PiKeeb/fu-keyboard/pcb_files/kicad_project/fu_keyboard.kicad_sch

## KiCad design pcb_files/kicad_project/fu_keyboard.kicad_sch (2021-12-26)

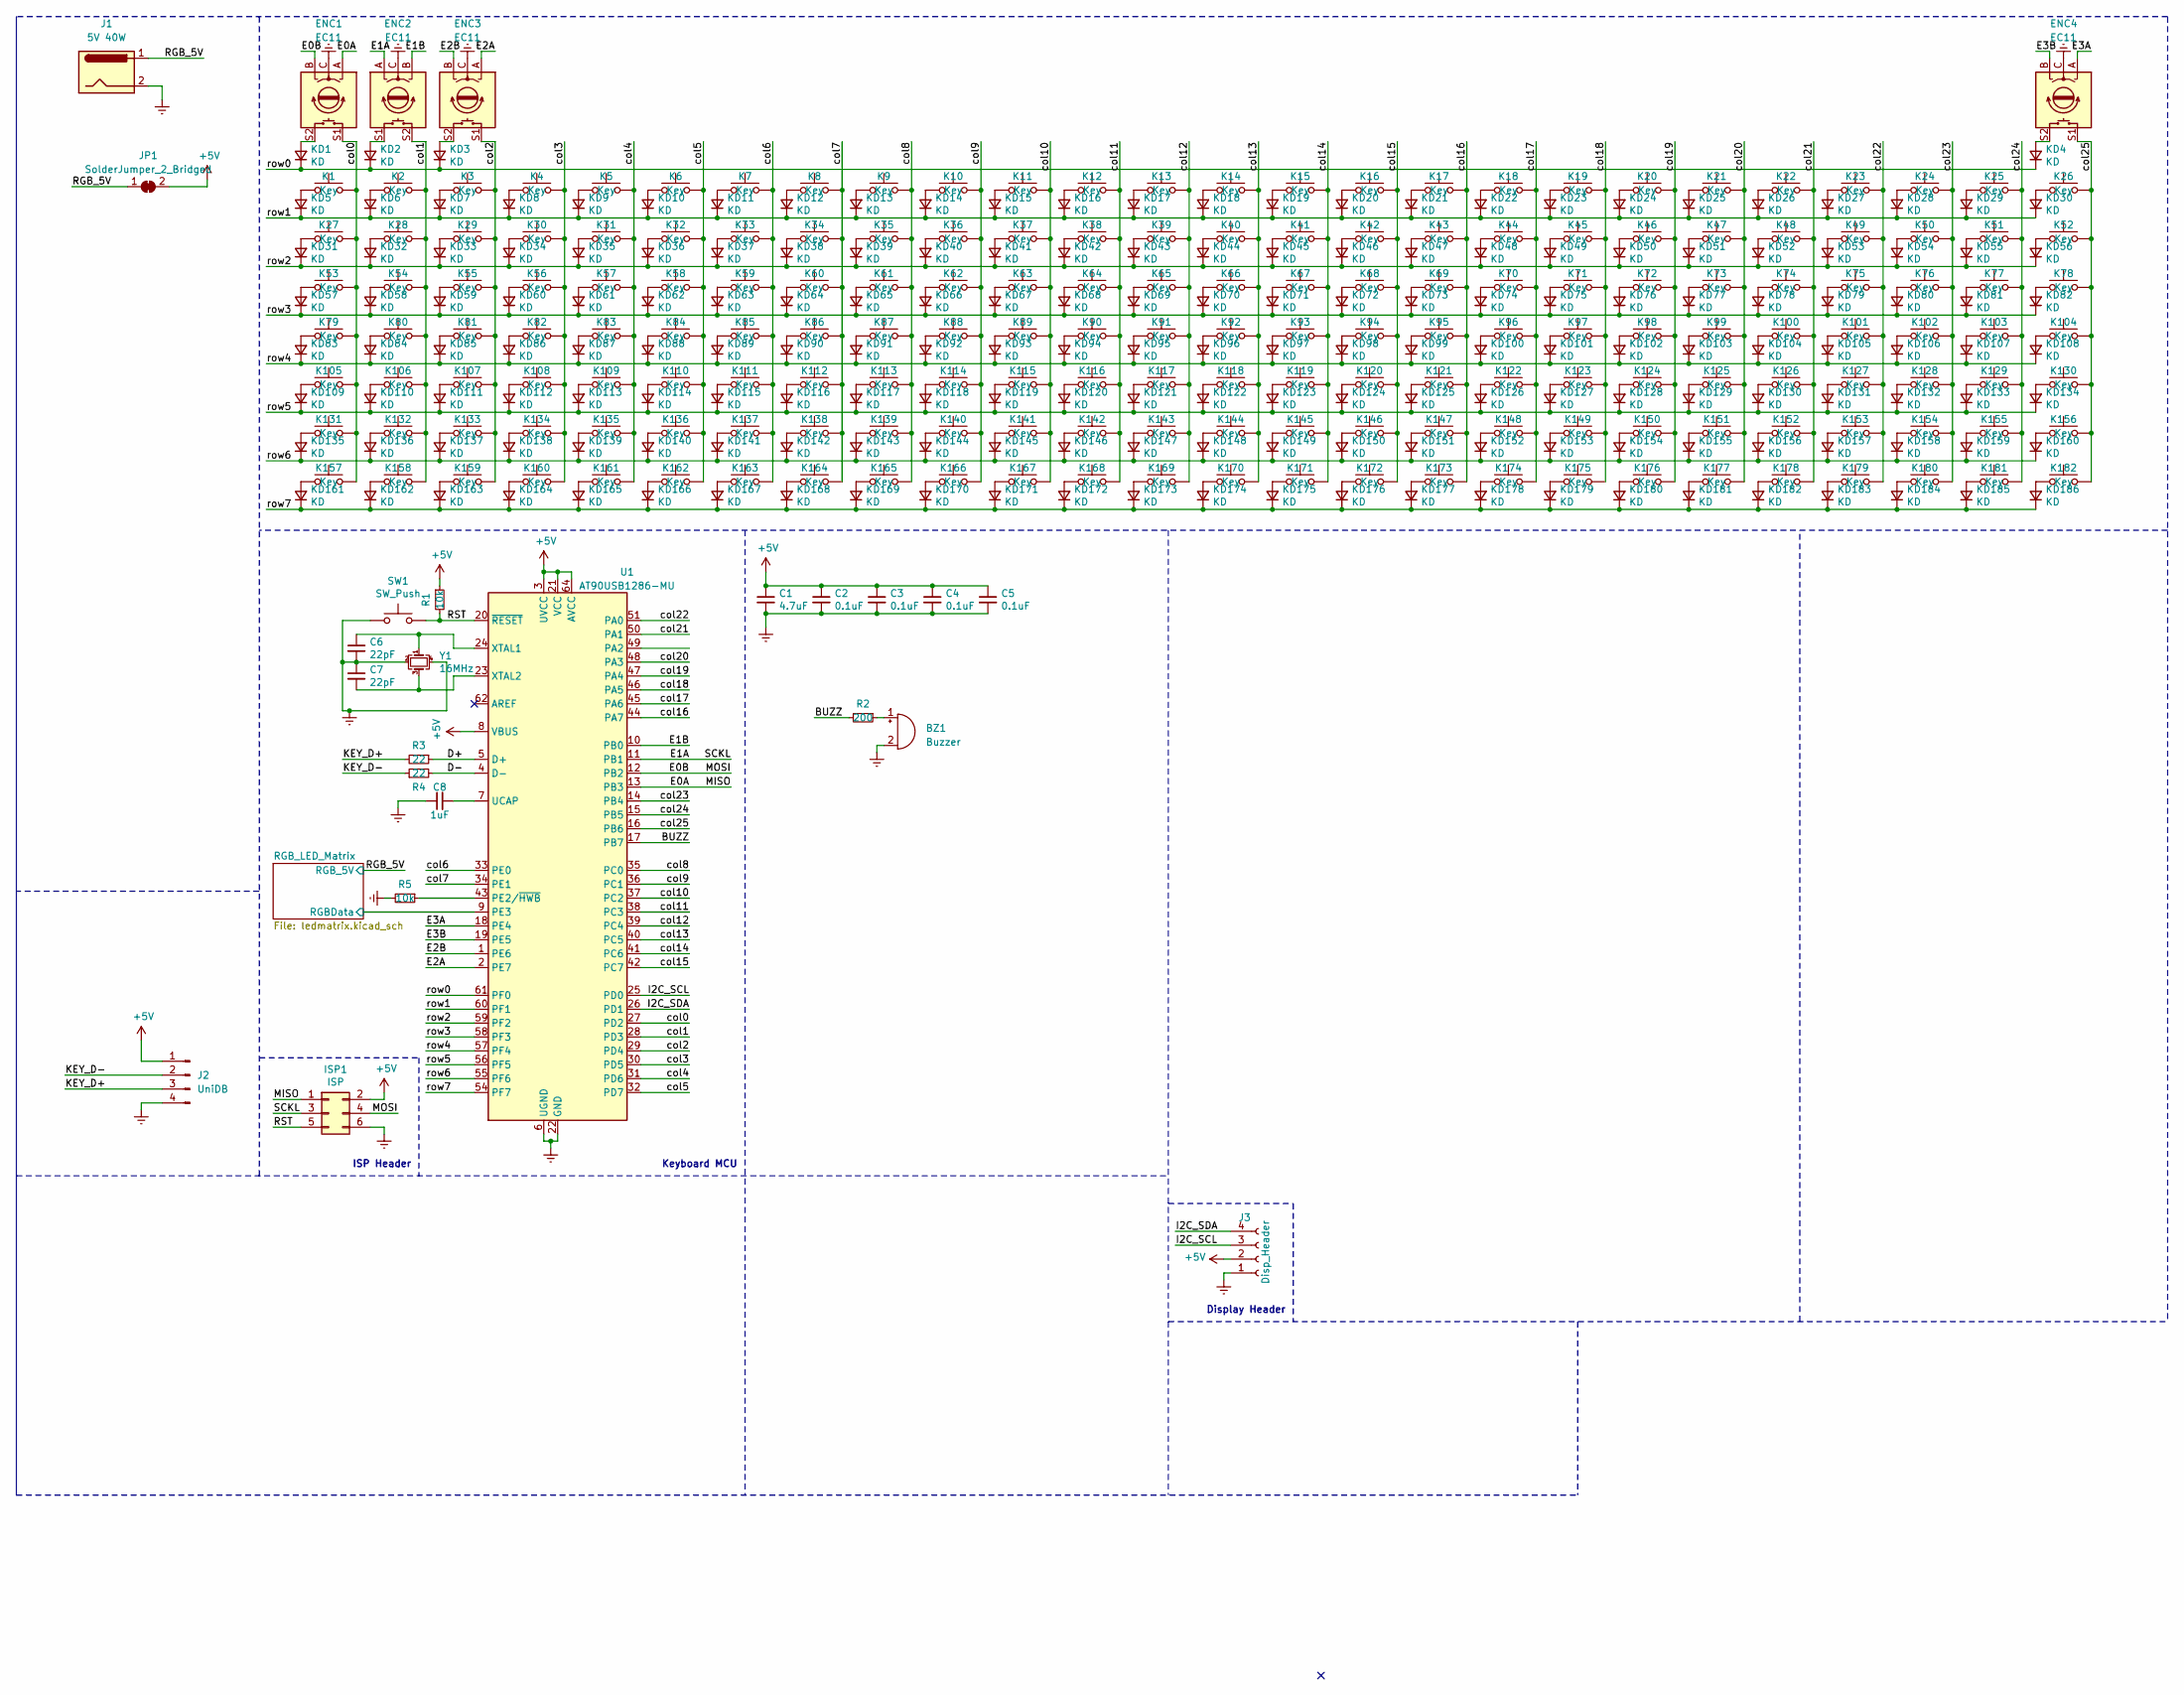
[picture p6: schematic fu_keyboard.kicad_sch]

Parts:
BZ1: Buzzer; Buzzer_CUI_CPT-9019S-SMT
C1: 4.7uF; C_0603_1608Metric
C2, C3, C4, C5: 0.1uF; C_0603_1608Metric
C6, C7: 22pF; C_0603_1608Metric
C8: 1uF; C_0603_1608Metric
ENC1, ENC2, ENC3, ENC4: EC11; RotaryEncoder_Alps_EC11E-Switch_Vertical_H20mm_CircularMoun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
ISP1: ISP; PinHeader_2x03_P2.54mm_Vertical
J1: 5V 40W; DC-058A-D010
J2: UniDB; JST_SH_SM04B-SRSS-TB_1x04-1MP_P1.00mm_Horizontal
J3: Disp_Header; Generic_SSD1306_0.91inch
JP1: SolderJumper_2_Bridged; SolderJumper-2_P1.3mm_Bridged2Bar_RoundedPad1.0x1.5mm
K1, K2, K3, K4, K5, K6, K7, K8, K9, K10, K11, K12, K13, K14, K15, K16, K17, K18, K19, K20, K21, K22, K23, K24, K25, K26, K27, K28, K29, K30, K31, K32, K33, K34, K35, K36, K37, K38, K39, K40, K41, K42, K43, K44, K45, K46, K47, K48, K49, K50, K51, K52, K53, K54, K55, K56, K57, K58, K59, K60, K61, K62, K63, K64, K65, K66, K67, K68, K69, K70, K71, K72, K73, K74, K75, K76, K77, K78, K79, K80, K81, K82, K83, K84, K85, K86, K87, K88, K89, K90, K91, K92, K93, K94, K95, K96, K97, K98, K99, K100, K101, K102, K103, K104, K105, K106, K107, K108, K109, K110, K111, K112, K113, K114, K115, K116, K117, K118, K119, K120, K121, K122, K123, K124, K125, K126, K127, K128, K129, K130, K131, K132, K133, K134, K135, K136, K137, K138, K139, K140, K141, K142, K143, K144, K145, K146, K147, K148, K149, K150, K151, K152, K153, K154, K155, K156, K157, K158, K159, K160, K161, K162, K163, K164, K165, K166, K167, K168, K169, K170, K171, K172, K173, K174, K175, K176, K177, K178, K179, K180, K181, K182: Key; Kailh_MX_Socket_1.00u_HoledPads
KD1, KD2, KD3, KD4, KD5, KD6, KD7, KD8, KD9, KD10, KD11, KD12, KD13, KD14, KD15, KD16, KD17, KD18, KD19, KD20, KD21, KD22, KD23, KD24, KD25, KD26, KD27, KD28, KD29, KD30, KD31, KD32, KD33, KD34, KD35, KD36, KD37, KD38, KD39, KD40, KD41, KD42, KD43, KD44, KD45, KD46, KD47, KD48, KD49, KD50, KD51, KD52, KD53, KD54, KD55, KD56, KD57, KD58, KD59, KD60, KD61, KD62, KD63, KD64, KD65, KD66, KD67, KD68, KD69, KD70, KD71, KD72, KD73, KD74, KD75, KD76, KD77, KD78, KD79, KD80, KD81, KD82, KD83, KD84, KD85, KD86, KD87, KD88, KD89, KD90, KD91, KD92, KD93, KD94, KD95, KD96, KD97, KD98, KD99, KD100, KD101, KD102, KD103, KD104, KD105, KD106, KD107, KD108, KD109, KD110, KD111, KD112, KD113, KD114, KD115, KD116, KD117, KD118, KD119, KD120, KD121, KD122, KD123, KD124, KD125, KD126, KD127, KD128, KD129, KD130, KD131, KD132, KD133, KD134, KD135, KD136, KD137, KD138, KD139, KD140, KD141, KD142, KD143, KD144, KD145, KD146, KD147, KD148, KD149, KD150, KD151, KD152, KD153, KD154, KD155, KD156, KD157, KD158, KD159, KD160, KD161, KD162, KD163, KD164, KD165, KD166, KD167, KD168, KD169, KD170, KD171, KD172, KD173, KD174, KD175, KD176, KD177, KD178, KD179, KD180, KD181, KD182, KD183, KD184, KD185, KD186: KD; D_0805_2012Metric
R1, R5: 10k; R_0603_1608Metric
R2: 200; R_0603_1608Metric
R3, R4: 22; R_0603_1608Metric
SW1: SW_Push; SW_SPST_TL3342
U1: AT90USB1286-MU; QFN-64-1EP_9x9mm_P0.5mm_EP7.5x7.5mm
Y1: 16MHz; Crystal_SMD_3225-4Pin_3.2x2.5mm

Connections:
+5V: C1.1, C2.1, C3.1, C4.1, C5.1, ISP1.2, J2.1, J3.2, JP1.2 (B), R1.1, U1.3 (UVCC), U1.8 (VBUS), U1.21 (VCC), U1.52 (VCC), U1.64 (AVCC)
BUZZ: R2.2, U1.17 (PB7)
D+: R3.1, U1.5 (D+)
D-: R4.2, U1.4 (D-)
E0A: ENC1.A, ISP1.1, U1.13 (PB3)
E0B: ENC1.B, ISP1.4, U1.12 (PB2)
E1A: ENC2.A, ISP1.3, U1.11 (PB1)
E1B: ENC2.B, U1.10 (PB0)
E2A: ENC3.A, U1.2 (PE7)
E2B: ENC3.B, U1.1 (PE6)
E3A: ENC4.A, U1.18 (PE4)
E3B: ENC4.B, U1.19 (PE5)
Earth: BZ1.2 (+), C1.2, C2.2, C3.2, C4.2, C5.2, C6.2, C7.1, C8.1, ENC1.C, ENC2.C, ENC3.C, ENC4.C, ISP1.6, J1.2, J2.4, J3.1, R5.2, SW1.1, U1.6 (UGND), U1.22 (GND), U1.53 (GND), U1.63 (GND), U1.65 (GND), Y1.2, Y1.4
I2C_SCL: J3.3, U1.25 (PD0)
I2C_SDA: J3.4, U1.26 (PD1)
KEY_D+: J2.3, R3.2
KEY_D-: J2.2, R4.1
unnamed: BZ1.1 (-), R2.1
unnamed: C6.1, U1.24 (XTAL1), Y1.1
unnamed: C7.2, U1.23 (XTAL2), Y1.3
unnamed: C8.2, U1.7 (UCAP)
unnamed: ENC1.S2, KD1.2 (A)
unnamed: ENC2.S1, KD2.2 (A)
unnamed: ENC3.S2, KD3.2 (A)
unnamed: ENC4.S2, KD4.2 (A)
unnamed: K1.1, KD5.2 (A)
unnamed: K2.1, KD6.2 (A)
unnamed: K3.1, KD7.2 (A)
unnamed: K4.1, KD8.2 (A)
unnamed: K5.1, KD9.2 (A)
unnamed: K6.1, KD10.2 (A)
unnamed: K7.1, KD11.2 (A)
unnamed: K8.1, KD12.2 (A)
unnamed: K9.1, KD13.2 (A)
unnamed: K10.1, KD14.2 (A)
unnamed: K11.1, KD15.2 (A)
unnamed: K12.1, KD16.2 (A)
unnamed: K13.1, KD17.2 (A)
unnamed: K14.1, KD18.2 (A)
unnamed: K15.1, KD19.2 (A)
unnamed: K16.1, KD20.2 (A)
unnamed: K17.1, KD21.2 (A)
unnamed: K18.1, KD22.2 (A)
unnamed: K19.1, KD23.2 (A)
unnamed: K20.1, KD24.2 (A)
unnamed: K21.1, KD25.2 (A)
unnamed: K22.1, KD26.2 (A)
unnamed: K23.1, KD27.2 (A)
unnamed: K24.1, KD28.2 (A)
unnamed: K25.1, KD29.2 (A)
unnamed: K26.1, KD30.2 (A)
unnamed: K27.1, KD31.2 (A)
unnamed: K28.1, KD32.2 (A)
unnamed: K29.1, KD33.2 (A)
unnamed: K30.1, KD34.2 (A)
unnamed: K31.1, KD35.2 (A)
unnamed: K32.1, KD36.2 (A)
unnamed: K33.1, KD37.2 (A)
unnamed: K34.1, KD38.2 (A)
unnamed: K35.1, KD39.2 (A)
unnamed: K36.1, KD40.2 (A)
unnamed: K37.1, KD41.2 (A)
unnamed: K38.1, KD42.2 (A)
unnamed: K39.1, KD43.2 (A)
unnamed: K40.1, KD44.2 (A)
unnamed: K41.1, KD45.2 (A)
unnamed: K42.1, KD46.2 (A)
unnamed: K43.1, KD47.2 (A)
unnamed: K44.1, KD48.2 (A)
unnamed: K45.1, KD49.2 (A)
unnamed: K46.1, KD50.2 (A)
unnamed: K47.1, KD51.2 (A)
unnamed: K48.1, KD52.2 (A)
unnamed: K49.1, KD53.2 (A)
unnamed: K50.1, KD54.2 (A)
unnamed: K51.1, KD55.2 (A)
unnamed: K52.1, KD56.2 (A)
unnamed: K53.1, KD57.2 (A)
unnamed: K54.1, KD58.2 (A)
unnamed: K55.1, KD59.2 (A)
unnamed: K56.1, KD60.2 (A)
unnamed: K57.1, KD61.2 (A)
unnamed: K58.1, KD62.2 (A)
unnamed: K59.1, KD63.2 (A)
unnamed: K60.1, KD64.2 (A)
unnamed: K61.1, KD65.2 (A)
unnamed: K62.1, KD66.2 (A)
unnamed: K63.1, KD67.2 (A)
unnamed: K64.1, KD68.2 (A)
unnamed: K65.1, KD69.2 (A)
unnamed: K66.1, KD70.2 (A)
unnamed: K67.1, KD71.2 (A)
unnamed: K68.1, KD72.2 (A)
unnamed: K69.1, KD73.2 (A)
unnamed: K70.1, KD74.2 (A)
unnamed: K71.1, KD75.2 (A)
unnamed: K72.1, KD76.2 (A)
unnamed: K73.1, KD77.2 (A)
unnamed: K74.1, KD78.2 (A)
unnamed: K75.1, KD79.2 (A)
unnamed: K76.1, KD80.2 (A)
unnamed: K77.1, KD81.2 (A)
unnamed: K78.1, KD82.2 (A)
unnamed: K79.1, KD83.2 (A)
unnamed: K80.1, KD84.2 (A)
unnamed: K81.1, KD85.2 (A)
unnamed: K82.1, KD86.2 (A)
unnamed: K83.1, KD87.2 (A)
unnamed: K84.1, KD88.2 (A)
unnamed: K85.1, KD89.2 (A)
unnamed: K86.1, KD90.2 (A)
unnamed: K87.1, KD91.2 (A)
unnamed: K88.1, KD92.2 (A)
unnamed: K89.1, KD93.2 (A)
unnamed: K90.1, KD94.2 (A)
unnamed: K91.1, KD95.2 (A)
unnamed: K92.1, KD96.2 (A)
unnamed: K93.1, KD97.2 (A)
unnamed: K94.1, KD98.2 (A)
unnamed: K95.1, KD99.2 (A)
unnamed: K96.1, KD100.2 (A)
unnamed: K97.1, KD101.2 (A)
unnamed: K98.1, KD102.2 (A)
unnamed: K99.1, KD103.2 (A)
unnamed: K100.1, KD104.2 (A)
unnamed: K101.1, KD105.2 (A)
unnamed: K102.1, KD106.2 (A)
unnamed: K103.1, KD107.2 (A)
unnamed: K104.1, KD108.2 (A)
unnamed: K105.1, KD109.2 (A)
unnamed: K106.1, KD110.2 (A)
unnamed: K107.1, KD111.2 (A)
unnamed: K108.1, KD112.2 (A)
unnamed: K109.1, KD113.2 (A)
unnamed: K110.1, KD114.2 (A)
unnamed: K111.1, KD115.2 (A)
unnamed: K112.1, KD116.2 (A)
unnamed: K113.1, KD117.2 (A)
unnamed: K114.1, KD118.2 (A)
unnamed: K115.1, KD119.2 (A)
unnamed: K116.1, KD120.2 (A)
unnamed: K117.1, KD121.2 (A)
unnamed: K118.1, KD122.2 (A)
unnamed: K119.1, KD123.2 (A)
unnamed: K120.1, KD124.2 (A)
unnamed: K121.1, KD125.2 (A)
unnamed: K122.1, KD126.2 (A)
unnamed: K123.1, KD127.2 (A)
unnamed: K124.1, KD128.2 (A)
unnamed: K125.1, KD129.2 (A)
unnamed: K126.1, KD130.2 (A)
unnamed: K127.1, KD131.2 (A)
unnamed: K128.1, KD132.2 (A)
unnamed: K129.1, KD133.2 (A)
unnamed: K130.1, KD134.2 (A)
unnamed: K131.1, KD135.2 (A)
unnamed: K132.1, KD136.2 (A)
unnamed: K133.1, KD137.2 (A)
unnamed: K134.1, KD138.2 (A)
unnamed: K135.1, KD139.2 (A)
unnamed: K136.1, KD140.2 (A)
unnamed: K137.1, KD141.2 (A)
unnamed: K138.1, KD142.2 (A)
unnamed: K139.1, KD143.2 (A)
unnamed: K140.1, KD144.2 (A)
unnamed: K141.1, KD145.2 (A)
unnamed: K142.1, KD146.2 (A)
unnamed: K143.1, KD147.2 (A)
unnamed: K144.1, KD148.2 (A)
unnamed: K145.1, KD149.2 (A)
unnamed: K146.1, KD150.2 (A)
unnamed: K147.1, KD151.2 (A)
unnamed: K148.1, KD152.2 (A)
unnamed: K149.1, KD153.2 (A)
unnamed: K150.1, KD154.2 (A)
unnamed: K151.1, KD155.2 (A)
unnamed: K152.1, KD156.2 (A)
unnamed: K153.1, KD157.2 (A)
unnamed: K154.1, KD158.2 (A)
unnamed: K155.1, KD159.2 (A)
unnamed: K156.1, KD160.2 (A)
unnamed: K157.1, KD161.2 (A)
unnamed: K158.1, KD162.2 (A)
unnamed: K159.1, KD163.2 (A)
unnamed: K160.1, KD164.2 (A)
unnamed: K161.1, KD165.2 (A)
unnamed: K162.1, KD166.2 (A)
unnamed: K163.1, KD167.2 (A)
unnamed: K164.1, KD168.2 (A)
unnamed: K165.1, KD169.2 (A)
unnamed: K166.1, KD170.2 (A)
unnamed: K167.1, KD171.2 (A)
unnamed: K168.1, KD172.2 (A)
unnamed: K169.1, KD173.2 (A)
unnamed: K170.1, KD174.2 (A)
unnamed: K171.1, KD175.2 (A)
unnamed: K172.1, KD176.2 (A)
unnamed: K173.1, KD177.2 (A)
unnamed: K174.1, KD178.2 (A)
unnamed: K175.1, KD179.2 (A)
unnamed: K176.1, KD180.2 (A)
unnamed: K177.1, KD181.2 (A)
unnamed: K178.1, KD182.2 (A)
unnamed: K179.1, KD183.2 (A)
unnamed: K180.1, KD184.2 (A)
unnamed: K181.1, KD185.2 (A)
unnamed: K182.1, KD186.2 (A)
unnamed: R5.1, U1.43 (PE2/~HWB)
RGBData: U1.9 (PE3)
RGB_5V: J1.1, JP1.1 (A)
RST: ISP1.5, R1.2, SW1.2, U1.20 (~RESET)
col0: ENC1.S1, K1.2, K27.2, K53.2, K79.2, K105.2, K131.2, K157.2, U1.27 (PD2)
col1: ENC2.S2, K2.2, K28.2, K54.2, K80.2, K106.2, K132.2, K158.2, U1.28 (PD3)
col2: ENC3.S1, K3.2, K29.2, K55.2, K81.2, K107.2, K133.2, K159.2, U1.29 (PD4)
col3: K4.2, K30.2, K56.2, K82.2, K108.2, K134.2, K160.2, U1.30 (PD5)
col4: K5.2, K31.2, K57.2, K83.2, K109.2, K135.2, K161.2, U1.31 (PD6)
col5: K6.2, K32.2, K58.2, K84.2, K110.2, K136.2, K162.2, U1.32 (PD7)
col6: K7.2, K33.2, K59.2, K85.2, K111.2, K137.2, K163.2, U1.33 (PE0)
col7: K8.2, K34.2, K60.2, K86.2, K112.2, K138.2, K164.2, U1.34 (PE1)
col8: K9.2, K35.2, K61.2, K87.2, K113.2, K139.2, K165.2, U1.35 (PC0)
col9: K10.2, K36.2, K62.2, K88.2, K114.2, K140.2, K166.2, U1.36 (PC1)
col10: K11.2, K37.2, K63.2, K89.2, K115.2, K141.2, K167.2, U1.37 (PC2)
col11: K12.2, K38.2, K64.2, K90.2, K116.2, K142.2, K168.2, U1.38 (PC3)
col12: K13.2, K39.2, K65.2, K91.2, K117.2, K143.2, K169.2, U1.39 (PC4)
col13: K14.2, K40.2, K66.2, K92.2, K118.2, K144.2, K170.2, U1.40 (PC5)
col14: K15.2, K41.2, K67.2, K93.2, K119.2, K145.2, K171.2, U1.41 (PC6)
col15: K16.2, K42.2, K68.2, K94.2, K120.2, K146.2, K172.2, U1.42 (PC7)
col16: K17.2, K43.2, K69.2, K95.2, K121.2, K147.2, K173.2, U1.44 (PA7)
col17: K18.2, K44.2, K70.2, K96.2, K122.2, K148.2, K174.2, U1.45 (PA6)
col18: K19.2, K45.2, K71.2, K97.2, K123.2, K149.2, K175.2, U1.46 (PA5)
col19: K20.2, K46.2, K72.2, K98.2, K124.2, K150.2, K176.2, U1.47 (PA4)
col20: K21.2, K47.2, K73.2, K99.2, K125.2, K151.2, K177.2, U1.48 (PA3)
col21: K22.2, K48.2, K74.2, K100.2, K126.2, K152.2, K178.2, U1.50 (PA1)
col22: K23.2, K49.2, K75.2, K101.2, K127.2, K153.2, K179.2, U1.51 (PA0)
col23: K24.2, K50.2, K76.2, K102.2, K128.2, K154.2, K180.2, U1.14 (PB4)
col24: K25.2, K51.2, K77.2, K103.2, K129.2, K155.2, K181.2, U1.15 (PB5)
col25: ENC4.S1, K26.2, K52.2, K78.2, K104.2, K130.2, K156.2, K182.2, U1.16 (PB6)
row0: KD1.1 (K), KD2.1 (K), KD3.1 (K), KD4.1 (K), U1.61 (PF0)
row1: KD5.1 (K), KD6.1 (K), KD7.1 (K), KD8.1 (K), KD9.1 (K), KD10.1 (K), KD11.1 (K), KD12.1 (K), KD13.1 (K), KD14.1 (K), KD15.1 (K), KD16.1 (K), KD17.1 (K), KD18.1 (K), KD19.1 (K), KD20.1 (K), KD21.1 (K), KD22.1 (K), KD23.1 (K), KD24.1 (K), KD25.1 (K), KD26.1 (K), KD27.1 (K), KD28.1 (K), KD29.1 (K), KD30.1 (K), U1.60 (PF1)
row2: KD31.1 (K), KD32.1 (K), KD33.1 (K), KD34.1 (K), KD35.1 (K), KD36.1 (K), KD37.1 (K), KD38.1 (K), KD39.1 (K), KD40.1 (K), KD41.1 (K), KD42.1 (K), KD43.1 (K), KD44.1 (K), KD45.1 (K), KD46.1 (K), KD47.1 (K), KD48.1 (K), KD49.1 (K), KD50.1 (K), KD51.1 (K), KD52.1 (K), KD53.1 (K), KD54.1 (K), KD55.1 (K), KD56.1 (K), U1.59 (PF2)
row3: KD57.1 (K), KD58.1 (K), KD59.1 (K), KD60.1 (K), KD61.1 (K), KD62.1 (K), KD63.1 (K), KD64.1 (K), KD65.1 (K), KD66.1 (K), KD67.1 (K), KD68.1 (K), KD69.1 (K), KD70.1 (K), KD71.1 (K), KD72.1 (K), KD73.1 (K), KD74.1 (K), KD75.1 (K), KD76.1 (K), KD77.1 (K), KD78.1 (K), KD79.1 (K), KD80.1 (K), KD81.1 (K), KD82.1 (K), U1.58 (PF3)
row4: KD83.1 (K), KD84.1 (K), KD85.1 (K), KD86.1 (K), KD87.1 (K), KD88.1 (K), KD89.1 (K), KD90.1 (K), KD91.1 (K), KD92.1 (K), KD93.1 (K), KD94.1 (K), KD95.1 (K), KD96.1 (K), KD97.1 (K), KD98.1 (K), KD99.1 (K), KD100.1 (K), KD101.1 (K), KD102.1 (K), KD103.1 (K), KD104.1 (K), KD105.1 (K), KD106.1 (K), KD107.1 (K), KD108.1 (K), U1.57 (PF4)
row5: KD109.1 (K), KD110.1 (K), KD111.1 (K), KD112.1 (K), KD113.1 (K), KD114.1 (K), KD115.1 (K), KD116.1 (K), KD117.1 (K), KD118.1 (K), KD119.1 (K), KD120.1 (K), KD121.1 (K), KD122.1 (K), KD123.1 (K), KD124.1 (K), KD125.1 (K), KD126.1 (K), KD127.1 (K), KD128.1 (K), KD129.1 (K), KD130.1 (K), KD131.1 (K), KD132.1 (K), KD133.1 (K), KD134.1 (K), U1.56 (PF5)
row6: KD135.1 (K), KD136.1 (K), KD137.1 (K), KD138.1 (K), KD139.1 (K), KD140.1 (K), KD141.1 (K), KD142.1 (K), KD143.1 (K), KD144.1 (K), KD145.1 (K), KD146.1 (K), KD147.1 (K), KD148.1 (K), KD149.1 (K), KD150.1 (K), KD151.1 (K), KD152.1 (K), KD153.1 (K), KD154.1 (K), KD155.1 (K), KD156.1 (K), KD157.1 (K), KD158.1 (K), KD159.1 (K), KD160.1 (K), U1.55 (PF6)
row7: KD161.1 (K), KD162.1 (K), KD163.1 (K), KD164.1 (K), KD165.1 (K), KD166.1 (K), KD167.1 (K), KD168.1 (K), KD169.1 (K), KD170.1 (K), KD171.1 (K), KD172.1 (K), KD173.1 (K), KD174.1 (K), KD175.1 (K), KD176.1 (K), KD177.1 (K), KD178.1 (K), KD179.1 (K), KD180.1 (K), KD181.1 (K), KD182.1 (K), KD183.1 (K), KD184.1 (K), KD185.1 (K), KD186.1 (K), U1.54 (PF7)

Notes on the sheet:
Keyboard MCU
ISP Header
Display Header
