PiKeeb/fu-keyboard/pcb_files/kicad_project/ledmatrix.kicad_sch

## KiCad design pcb_files/kicad_project/ledmatrix.kicad_sch (2021-12-26)

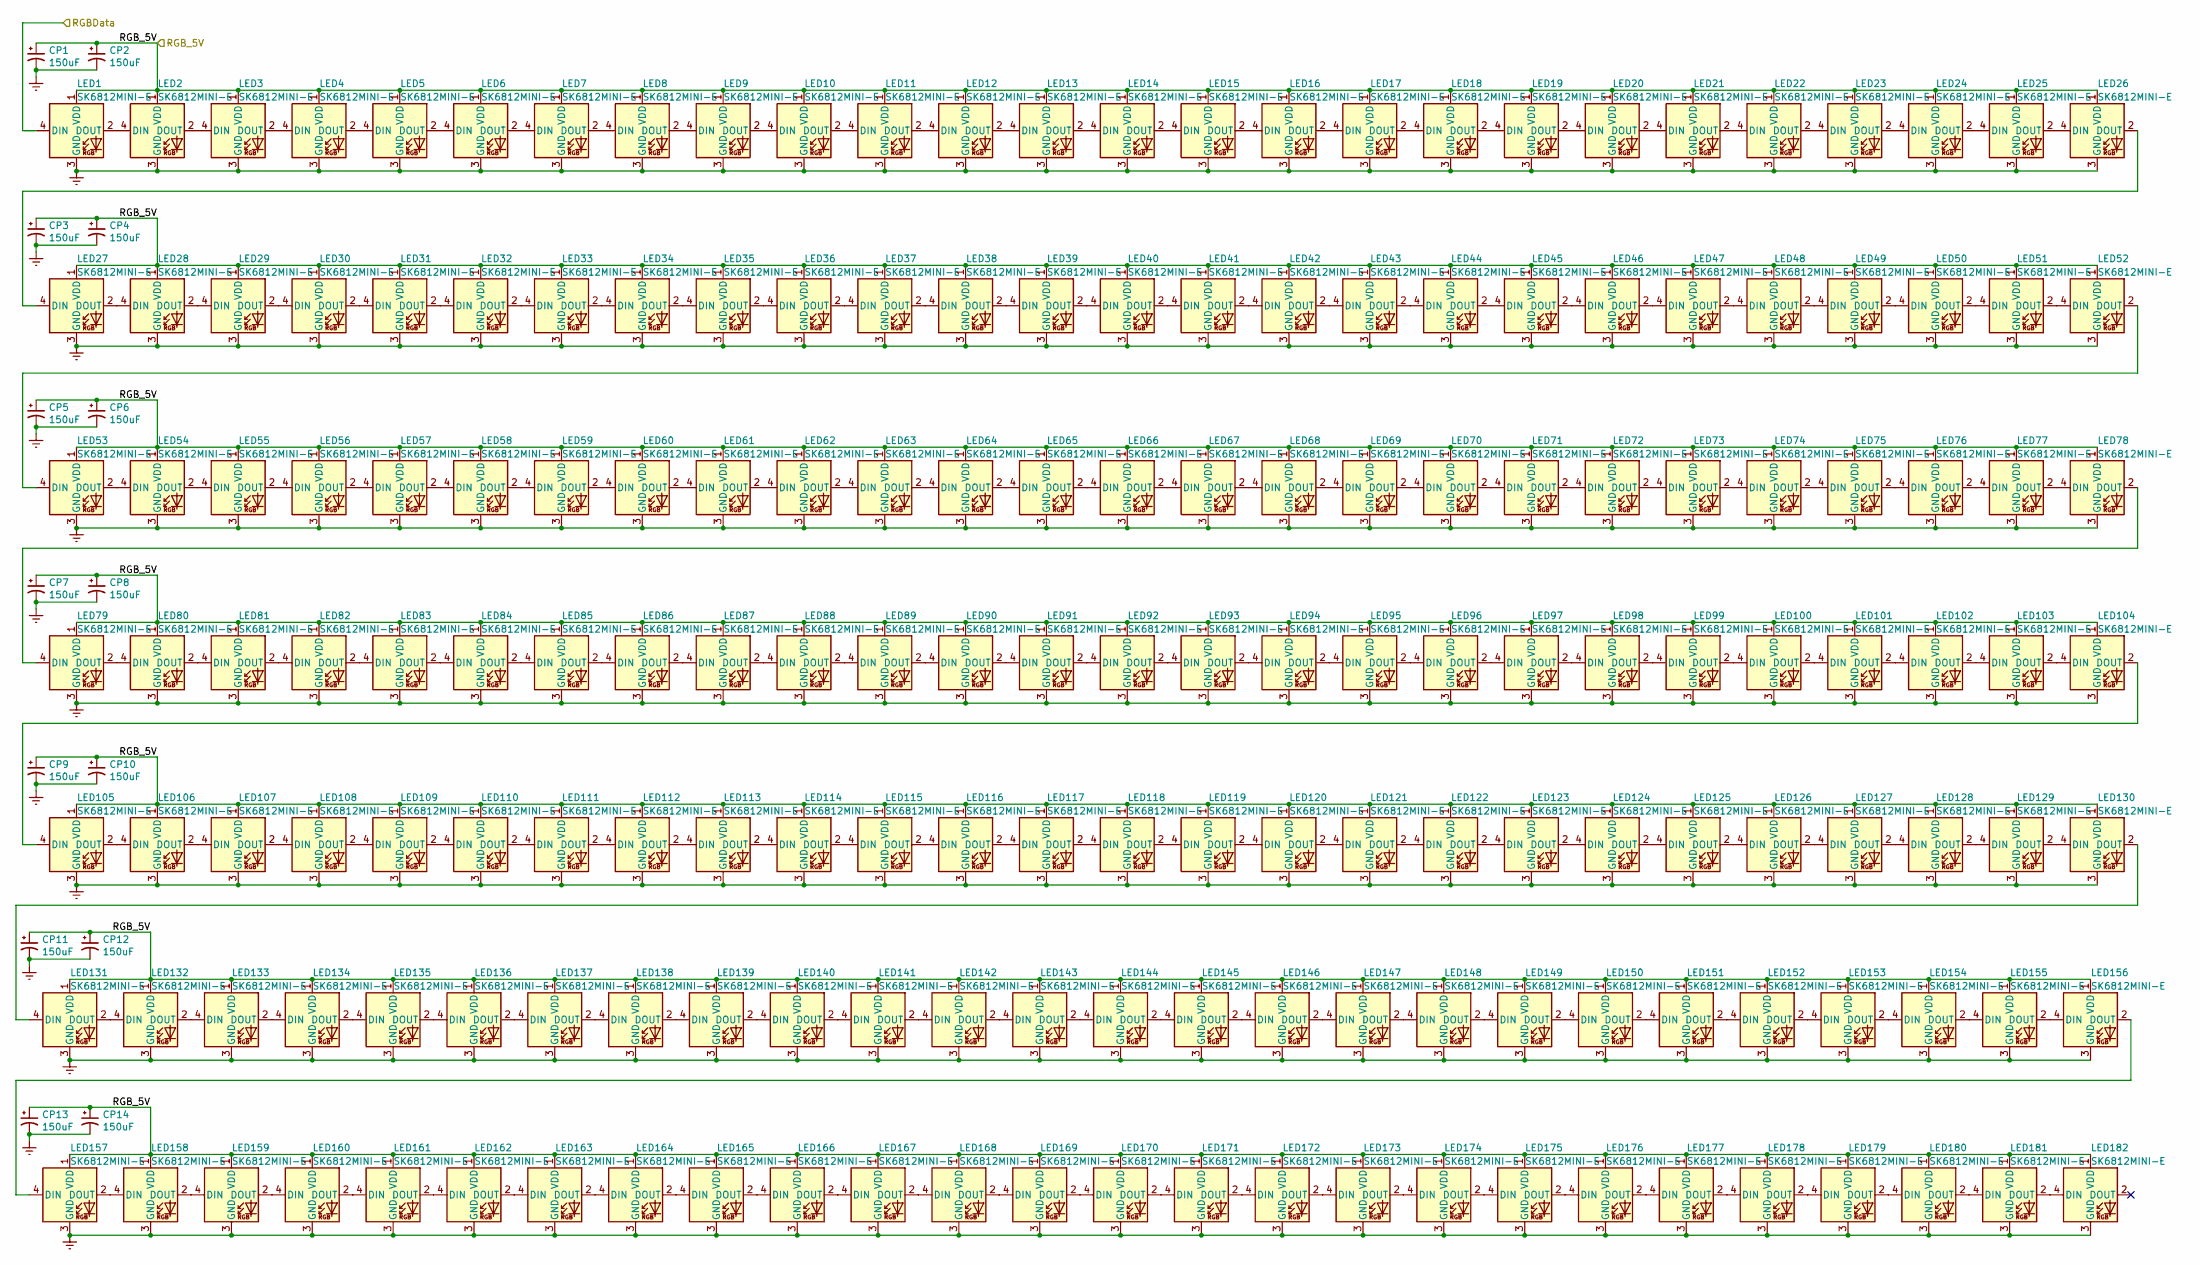
[picture p7: schematic ledmatrix.kicad_sch]

Parts:
CP1, CP2, CP3, CP4, CP5, CP6, CP7, CP8, CP9, CP10, CP11, CP12, CP13, CP14: 150uF; CP_EIA-3528-21_Kemet-B
LED1, LED2, LED3, LED4, LED5, LED6, LED7, LED8, LED9, LED10, LED11, LED12, LED13, LED14, LED15, LED16, LED17, LED18, LED19, LED20, LED21, LED22, LED23, LED24, LED25, LED26, LED54, LED55, LED56, LED57, LED58, LED59, LED60, LED61, LED62, LED63, LED64, LED65, LED66, LED67, LED68, LED69, LED70, LED71, LED72, LED73, LED74, LED75, LED76, LED77, LED78, LED79, LED106, LED107, LED108, LED109, LED110, LED111, LED112, LED113, LED114, LED115, LED116, LED117, LED118, LED119, LED120, LED121, LED122, LED123, LED124, LED125, LED126, LED127, LED128, LED129, LED130, LED131, LED157, LED158, LED159, LED160, LED161, LED162, LED163, LED164, LED165, LED166, LED167, LED168, LED169, LED170, LED171, LED172, LED173, LED174, LED175, LED176, LED177, LED178, LED179, LED180, LED181, LED182: SK6812MINI-E; MX_SK6812MINI-E
LED27, LED28, LED29, LED30, LED31, LED32, LED33, LED34, LED35, LED36, LED37, LED38, LED39, LED40, LED41, LED42, LED43, LED44, LED45, LED46, LED47, LED48, LED49, LED50, LED51, LED52, LED53, LED80, LED81, LED82, LED83, LED84, LED85, LED86, LED87, LED88, LED89, LED90, LED91, LED92, LED93, LED94, LED95, LED96, LED97, LED98, LED99, LED100, LED101, LED102, LED103, LED104, LED105, LED132, LED133, LED134, LED135, LED136, LED137, LED138, LED139, LED140, LED141, LED142, LED143, LED144, LED145, LED146, LED147, LED148, LED149, LED150, LED151, LED152, LED153, LED154, LED155, LED156: SK6812MINI-E; MX_SK6812MINI-E_REV

Connections:
Earth: CP1.2, CP2.2, CP3.2, CP4.2, CP5.2, CP6.2, CP7.2, CP8.2, CP9.2, CP10.2, CP11.2, CP12.2, CP13.2, CP14.2, LED1.3 (GND), LED2.3 (GND), LED3.3 (GND), LED4.3 (GND), LED5.3 (GND), LED6.3 (GND), LED7.3 (GND), LED8.3 (GND), LED9.3 (GND), LED10.3 (GND), LED11.3 (GND), LED12.3 (GND), LED13.3 (GND), LED14.3 (GND), LED15.3 (GND), LED16.3 (GND), LED17.3 (GND), LED18.3 (GND), LED19.3 (GND), LED20.3 (GND), LED21.3 (GND), LED22.3 (GND), LED23.3 (GND), LED24.3 (GND), LED25.3 (GND), LED26.3 (GND), LED27.3 (GND), LED28.3 (GND), LED29.3 (GND), LED30.3 (GND), LED31.3 (GND), LED32.3 (GND), LED33.3 (GND), LED34.3 (GND), LED35.3 (GND), LED36.3 (GND), LED37.3 (GND), LED38.3 (GND), LED39.3 (GND), LED40.3 (GND), LED41.3 (GND), LED42.3 (GND), LED43.3 (GND), LED44.3 (GND), LED45.3 (GND), LED46.3 (GND), LED47.3 (GND), LED48.3 (GND), LED49.3 (GND), LED50.3 (GND), LED51.3 (GND), LED52.3 (GND), LED53.3 (GND), LED54.3 (GND), LED55.3 (GND), LED56.3 (GND), LED57.3 (GND), LED58.3 (GND), LED59.3 (GND), LED60.3 (GND), LED61.3 (GND), LED62.3 (GND), LED63.3 (GND), LED64.3 (GND), LED65.3 (GND), LED66.3 (GND), LED67.3 (GND), LED68.3 (GND), LED69.3 (GND), LED70.3 (GND), LED71.3 (GND), LED72.3 (GND), LED73.3 (GND), LED74.3 (GND), LED75.3 (GND), LED76.3 (GND), LED77.3 (GND), LED78.3 (GND), LED79.3 (GND), LED80.3 (GND), LED81.3 (GND), LED82.3 (GND), LED83.3 (GND), LED84.3 (GND), LED85.3 (GND), LED86.3 (GND), LED87.3 (GND), LED88.3 (GND), LED89.3 (GND), LED90.3 (GND), LED91.3 (GND), LED92.3 (GND), LED93.3 (GND), LED94.3 (GND), LED95.3 (GND), LED96.3 (GND), LED97.3 (GND), LED98.3 (GND), LED99.3 (GND), LED100.3 (GND), LED101.3 (GND), LED102.3 (GND), LED103.3 (GND), LED104.3 (GND), LED105.3 (GND), LED106.3 (GND), LED107.3 (GND), LED108.3 (GND), LED109.3 (GND), LED110.3 (GND), LED111.3 (GND), LED112.3 (GND), LED113.3 (GND), LED114.3 (GND), LED115.3 (GND), LED116.3 (GND), LED117.3 (GND), LED118.3 (GND), LED119.3 (GND), LED120.3 (GND), LED121.3 (GND), LED122.3 (GND), LED123.3 (GND), LED124.3 (GND), LED125.3 (GND), LED126.3 (GND), LED127.3 (GND), LED128.3 (GND), LED129.3 (GND), LED130.3 (GND), LED131.3 (GND), LED132.3 (GND), LED133.3 (GND), LED134.3 (GND), LED135.3 (GND), LED136.3 (GND), LED137.3 (GND), LED138.3 (GND), LED139.3 (GND), LED140.3 (GND), LED141.3 (GND), LED142.3 (GND), LED143.3 (GND), LED144.3 (GND), LED145.3 (GND), LED146.3 (GND), LED147.3 (GND), LED148.3 (GND), LED149.3 (GND), LED150.3 (GND), LED151.3 (GND), LED152.3 (GND), LED153.3 (GND), LED154.3 (GND), LED155.3 (GND), LED156.3 (GND), LED157.3 (GND), LED158.3 (GND), LED159.3 (GND), LED160.3 (GND), LED161.3 (GND), LED162.3 (GND), LED163.3 (GND), LED164.3 (GND), LED165.3 (GND), LED166.3 (GND), LED167.3 (GND), LED168.3 (GND), LED169.3 (GND), LED170.3 (GND), LED171.3 (GND), LED172.3 (GND), LED173.3 (GND), LED174.3 (GND), LED175.3 (GND), LED176.3 (GND), LED177.3 (GND), LED178.3 (GND), LED179.3 (GND), LED180.3 (GND), LED181.3 (GND), LED182.3 (GND)
unnamed: LED1.2 (DOUT), LED2.4 (DIN)
unnamed: LED2.2 (DOUT), LED3.4 (DIN)
unnamed: LED3.2 (DOUT), LED4.4 (DIN)
unnamed: LED4.2 (DOUT), LED5.4 (DIN)
unnamed: LED5.2 (DOUT), LED6.4 (DIN)
unnamed: LED6.2 (DOUT), LED7.4 (DIN)
unnamed: LED7.2 (DOUT), LED8.4 (DIN)
unnamed: LED8.2 (DOUT), LED9.4 (DIN)
unnamed: LED10.2 (DOUT), LED11.4 (DIN)
unnamed: LED9.2 (DOUT), LED10.4 (DIN)
unnamed: LED11.2 (DOUT), LED12.4 (DIN)
unnamed: LED12.2 (DOUT), LED13.4 (DIN)
unnamed: LED13.2 (DOUT), LED14.4 (DIN)
unnamed: LED14.2 (DOUT), LED15.4 (DIN)
unnamed: LED15.2 (DOUT), LED16.4 (DIN)
unnamed: LED16.2 (DOUT), LED17.4 (DIN)
unnamed: LED17.2 (DOUT), LED18.4 (DIN)
unnamed: LED18.2 (DOUT), LED19.4 (DIN)
unnamed: LED19.2 (DOUT), LED20.4 (DIN)
unnamed: LED20.2 (DOUT), LED21.4 (DIN)
unnamed: LED21.2 (DOUT), LED22.4 (DIN)
unnamed: LED22.2 (DOUT), LED23.4 (DIN)
unnamed: LED23.2 (DOUT), LED24.4 (DIN)
unnamed: LED24.2 (DOUT), LED25.4 (DIN)
unnamed: LED25.2 (DOUT), LED26.4 (DIN)
unnamed: LED26.2 (DOUT), LED27.4 (DIN)
unnamed: LED27.2 (DOUT), LED28.4 (DIN)
unnamed: LED28.2 (DOUT), LED29.4 (DIN)
unnamed: LED29.2 (DOUT), LED30.4 (DIN)
unnamed: LED30.2 (DOUT), LED31.4 (DIN)
unnamed: LED31.2 (DOUT), LED32.4 (DIN)
unnamed: LED32.2 (DOUT), LED33.4 (DIN)
unnamed: LED33.2 (DOUT), LED34.4 (DIN)
unnamed: LED34.2 (DOUT), LED35.4 (DIN)
unnamed: LED35.2 (DOUT), LED36.4 (DIN)
unnamed: LED36.2 (DOUT), LED37.4 (DIN)
unnamed: LED37.2 (DOUT), LED38.4 (DIN)
unnamed: LED38.2 (DOUT), LED39.4 (DIN)
unnamed: LED39.2 (DOUT), LED40.4 (DIN)
unnamed: LED40.2 (DOUT), LED41.4 (DIN)
unnamed: LED41.2 (DOUT), LED42.4 (DIN)
unnamed: LED42.2 (DOUT), LED43.4 (DIN)
unnamed: LED43.2 (DOUT), LED44.4 (DIN)
unnamed: LED44.2 (DOUT), LED45.4 (DIN)
unnamed: LED45.2 (DOUT), LED46.4 (DIN)
unnamed: LED46.2 (DOUT), LED47.4 (DIN)
unnamed: LED47.2 (DOUT), LED48.4 (DIN)
unnamed: LED48.2 (DOUT), LED49.4 (DIN)
unnamed: LED49.2 (DOUT), LED50.4 (DIN)
unnamed: LED50.2 (DOUT), LED51.4 (DIN)
unnamed: LED51.2 (DOUT), LED52.4 (DIN)
unnamed: LED52.2 (DOUT), LED53.4 (DIN)
unnamed: LED53.2 (DOUT), LED54.4 (DIN)
unnamed: LED54.2 (DOUT), LED55.4 (DIN)
unnamed: LED55.2 (DOUT), LED56.4 (DIN)
unnamed: LED56.2 (DOUT), LED57.4 (DIN)
unnamed: LED57.2 (DOUT), LED58.4 (DIN)
unnamed: LED58.2 (DOUT), LED59.4 (DIN)
unnamed: LED59.2 (DOUT), LED60.4 (DIN)
unnamed: LED60.2 (DOUT), LED61.4 (DIN)
unnamed: LED61.2 (DOUT), LED62.4 (DIN)
unnamed: LED62.2 (DOUT), LED63.4 (DIN)
unnamed: LED63.2 (DOUT), LED64.4 (DIN)
unnamed: LED64.2 (DOUT), LED65.4 (DIN)
unnamed: LED65.2 (DOUT), LED66.4 (DIN)
unnamed: LED66.2 (DOUT), LED67.4 (DIN)
unnamed: LED67.2 (DOUT), LED68.4 (DIN)
unnamed: LED68.2 (DOUT), LED69.4 (DIN)
unnamed: LED69.2 (DOUT), LED70.4 (DIN)
unnamed: LED70.2 (DOUT), LED71.4 (DIN)
unnamed: LED71.2 (DOUT), LED72.4 (DIN)
unnamed: LED72.2 (DOUT), LED73.4 (DIN)
unnamed: LED73.2 (DOUT), LED74.4 (DIN)
unnamed: LED74.2 (DOUT), LED75.4 (DIN)
unnamed: LED75.2 (DOUT), LED76.4 (DIN)
unnamed: LED76.2 (DOUT), LED77.4 (DIN)
unnamed: LED77.2 (DOUT), LED78.4 (DIN)
unnamed: LED78.2 (DOUT), LED79.4 (DIN)
unnamed: LED79.2 (DOUT), LED80.4 (DIN)
unnamed: LED80.2 (DOUT), LED81.4 (DIN)
unnamed: LED81.2 (DOUT), LED82.4 (DIN)
unnamed: LED82.2 (DOUT), LED83.4 (DIN)
unnamed: LED83.2 (DOUT), LED84.4 (DIN)
unnamed: LED84.2 (DOUT), LED85.4 (DIN)
unnamed: LED85.2 (DOUT), LED86.4 (DIN)
unnamed: LED86.2 (DOUT), LED87.4 (DIN)
unnamed: LED87.2 (DOUT), LED88.4 (DIN)
unnamed: LED88.2 (DOUT), LED89.4 (DIN)
unnamed: LED89.2 (DOUT), LED90.4 (DIN)
unnamed: LED90.2 (DOUT), LED91.4 (DIN)
unnamed: LED91.2 (DOUT), LED92.4 (DIN)
unnamed: LED92.2 (DOUT), LED93.4 (DIN)
unnamed: LED93.2 (DOUT), LED94.4 (DIN)
unnamed: LED94.2 (DOUT), LED95.4 (DIN)
unnamed: LED95.2 (DOUT), LED96.4 (DIN)
unnamed: LED96.2 (DOUT), LED97.4 (DIN)
unnamed: LED97.2 (DOUT), LED98.4 (DIN)
unnamed: LED98.2 (DOUT), LED99.4 (DIN)
unnamed: LED100.2 (DOUT), LED101.4 (DIN)
unnamed: LED99.2 (DOUT), LED100.4 (DIN)
unnamed: LED101.2 (DOUT), LED102.4 (DIN)
unnamed: LED102.2 (DOUT), LED103.4 (DIN)
unnamed: LED103.2 (DOUT), LED104.4 (DIN)
unnamed: LED104.2 (DOUT), LED105.4 (DIN)
unnamed: LED105.2 (DOUT), LED106.4 (DIN)
unnamed: LED106.2 (DOUT), LED107.4 (DIN)
unnamed: LED107.2 (DOUT), LED108.4 (DIN)
unnamed: LED108.2 (DOUT), LED109.4 (DIN)
unnamed: LED109.2 (DOUT), LED110.4 (DIN)
unnamed: LED110.2 (DOUT), LED111.4 (DIN)
unnamed: LED111.2 (DOUT), LED112.4 (DIN)
unnamed: LED112.2 (DOUT), LED113.4 (DIN)
unnamed: LED113.2 (DOUT), LED114.4 (DIN)
unnamed: LED114.2 (DOUT), LED115.4 (DIN)
unnamed: LED115.2 (DOUT), LED116.4 (DIN)
unnamed: LED116.2 (DOUT), LED117.4 (DIN)
unnamed: LED117.2 (DOUT), LED118.4 (DIN)
unnamed: LED118.2 (DOUT), LED119.4 (DIN)
unnamed: LED119.2 (DOUT), LED120.4 (DIN)
unnamed: LED120.2 (DOUT), LED121.4 (DIN)
unnamed: LED121.2 (DOUT), LED122.4 (DIN)
unnamed: LED122.2 (DOUT), LED123.4 (DIN)
unnamed: LED123.2 (DOUT), LED124.4 (DIN)
unnamed: LED124.2 (DOUT), LED125.4 (DIN)
unnamed: LED125.2 (DOUT), LED126.4 (DIN)
unnamed: LED126.2 (DOUT), LED127.4 (DIN)
unnamed: LED127.2 (DOUT), LED128.4 (DIN)
unnamed: LED128.2 (DOUT), LED129.4 (DIN)
unnamed: LED129.2 (DOUT), LED130.4 (DIN)
unnamed: LED130.2 (DOUT), LED131.4 (DIN)
unnamed: LED131.2 (DOUT), LED132.4 (DIN)
unnamed: LED132.2 (DOUT), LED133.4 (DIN)
unnamed: LED133.2 (DOUT), LED134.4 (DIN)
unnamed: LED134.2 (DOUT), LED135.4 (DIN)
unnamed: LED135.2 (DOUT), LED136.4 (DIN)
unnamed: LED136.2 (DOUT), LED137.4 (DIN)
unnamed: LED137.2 (DOUT), LED138.4 (DIN)
unnamed: LED138.2 (DOUT), LED139.4 (DIN)
unnamed: LED139.2 (DOUT), LED140.4 (DIN)
unnamed: LED140.2 (DOUT), LED141.4 (DIN)
unnamed: LED141.2 (DOUT), LED142.4 (DIN)
unnamed: LED142.2 (DOUT), LED143.4 (DIN)
unnamed: LED143.2 (DOUT), LED144.4 (DIN)
unnamed: LED144.2 (DOUT), LED145.4 (DIN)
unnamed: LED145.2 (DOUT), LED146.4 (DIN)
unnamed: LED146.2 (DOUT), LED147.4 (DIN)
unnamed: LED147.2 (DOUT), LED148.4 (DIN)
unnamed: LED148.2 (DOUT), LED149.4 (DIN)
unnamed: LED149.2 (DOUT), LED150.4 (DIN)
unnamed: LED150.2 (DOUT), LED151.4 (DIN)
unnamed: LED151.2 (DOUT), LED152.4 (DIN)
unnamed: LED152.2 (DOUT), LED153.4 (DIN)
unnamed: LED153.2 (DOUT), LED154.4 (DIN)
unnamed: LED154.2 (DOUT), LED155.4 (DIN)
unnamed: LED155.2 (DOUT), LED156.4 (DIN)
unnamed: LED156.2 (DOUT), LED157.4 (DIN)
unnamed: LED157.2 (DOUT), LED158.4 (DIN)
unnamed: LED158.2 (DOUT), LED159.4 (DIN)
unnamed: LED159.2 (DOUT), LED160.4 (DIN)
unnamed: LED160.2 (DOUT), LED161.4 (DIN)
unnamed: LED161.2 (DOUT), LED162.4 (DIN)
unnamed: LED162.2 (DOUT), LED163.4 (DIN)
unnamed: LED163.2 (DOUT), LED164.4 (DIN)
unnamed: LED164.2 (DOUT), LED165.4 (DIN)
unnamed: LED165.2 (DOUT), LED166.4 (DIN)
unnamed: LED166.2 (DOUT), LED167.4 (DIN)
unnamed: LED167.2 (DOUT), LED168.4 (DIN)
unnamed: LED168.2 (DOUT), LED169.4 (DIN)
unnamed: LED169.2 (DOUT), LED170.4 (DIN)
unnamed: LED170.2 (DOUT), LED171.4 (DIN)
unnamed: LED171.2 (DOUT), LED172.4 (DIN)
unnamed: LED172.2 (DOUT), LED173.4 (DIN)
unnamed: LED173.2 (DOUT), LED174.4 (DIN)
unnamed: LED174.2 (DOUT), LED175.4 (DIN)
unnamed: LED175.2 (DOUT), LED176.4 (DIN)
unnamed: LED176.2 (DOUT), LED177.4 (DIN)
unnamed: LED177.2 (DOUT), LED178.4 (DIN)
unnamed: LED178.2 (DOUT), LED179.4 (DIN)
unnamed: LED179.2 (DOUT), LED180.4 (DIN)
unnamed: LED180.2 (DOUT), LED181.4 (DIN)
unnamed: LED181.2 (DOUT), LED182.4 (DIN)
RGBData: LED1.4 (DIN)
RGB_5V: CP1.1, CP2.1, CP3.1, CP4.1, CP5.1, CP6.1, CP7.1, CP8.1, CP9.1, CP10.1, CP11.1, CP12.1, CP13.1, CP14.1, LED1.1 (VDD), LED2.1 (VDD), LED3.1 (VDD), LED4.1 (VDD), LED5.1 (VDD), LED6.1 (VDD), LED7.1 (VDD), LED8.1 (VDD), LED9.1 (VDD), LED10.1 (VDD), LED11.1 (VDD), LED12.1 (VDD), LED13.1 (VDD), LED14.1 (VDD), LED15.1 (VDD), LED16.1 (VDD), LED17.1 (VDD), LED18.1 (VDD), LED19.1 (VDD), LED20.1 (VDD), LED21.1 (VDD), LED22.1 (VDD), LED23.1 (VDD), LED24.1 (VDD), LED25.1 (VDD), LED26.1 (VDD), LED27.1 (VDD), LED28.1 (VDD), LED29.1 (VDD), LED30.1 (VDD), LED31.1 (VDD), LED32.1 (VDD), LED33.1 (VDD), LED34.1 (VDD), LED35.1 (VDD), LED36.1 (VDD), LED37.1 (VDD), LED38.1 (VDD), LED39.1 (VDD), LED40.1 (VDD), LED41.1 (VDD), LED42.1 (VDD), LED43.1 (VDD), LED44.1 (VDD), LED45.1 (VDD), LED46.1 (VDD), LED47.1 (VDD), LED48.1 (VDD), LED49.1 (VDD), LED50.1 (VDD), LED51.1 (VDD), LED52.1 (VDD), LED53.1 (VDD), LED54.1 (VDD), LED55.1 (VDD), LED56.1 (VDD), LED57.1 (VDD), LED58.1 (VDD), LED59.1 (VDD), LED60.1 (VDD), LED61.1 (VDD), LED62.1 (VDD), LED63.1 (VDD), LED64.1 (VDD), LED65.1 (VDD), LED66.1 (VDD), LED67.1 (VDD), LED68.1 (VDD), LED69.1 (VDD), LED70.1 (VDD), LED71.1 (VDD), LED72.1 (VDD), LED73.1 (VDD), LED74.1 (VDD), LED75.1 (VDD), LED76.1 (VDD), LED77.1 (VDD), LED78.1 (VDD), LED79.1 (VDD), LED80.1 (VDD), LED81.1 (VDD), LED82.1 (VDD), LED83.1 (VDD), LED84.1 (VDD), LED85.1 (VDD), LED86.1 (VDD), LED87.1 (VDD), LED88.1 (VDD), LED89.1 (VDD), LED90.1 (VDD), LED91.1 (VDD), LED92.1 (VDD), LED93.1 (VDD), LED94.1 (VDD), LED95.1 (VDD), LED96.1 (VDD), LED97.1 (VDD), LED98.1 (VDD), LED99.1 (VDD), LED100.1 (VDD), LED101.1 (VDD), LED102.1 (VDD), LED103.1 (VDD), LED104.1 (VDD), LED105.1 (VDD), LED106.1 (VDD), LED107.1 (VDD), LED108.1 (VDD), LED109.1 (VDD), LED110.1 (VDD), LED111.1 (VDD), LED112.1 (VDD), LED113.1 (VDD), LED114.1 (VDD), LED115.1 (VDD), LED116.1 (VDD), LED117.1 (VDD), LED118.1 (VDD), LED119.1 (VDD), LED120.1 (VDD), LED121.1 (VDD), LED122.1 (VDD), LED123.1 (VDD), LED124.1 (VDD), LED125.1 (VDD), LED126.1 (VDD), LED127.1 (VDD), LED128.1 (VDD), LED129.1 (VDD), LED130.1 (VDD), LED131.1 (VDD), LED132.1 (VDD), LED133.1 (VDD), LED134.1 (VDD), LED135.1 (VDD), LED136.1 (VDD), LED137.1 (VDD), LED138.1 (VDD), LED139.1 (VDD), LED140.1 (VDD), LED141.1 (VDD), LED142.1 (VDD), LED143.1 (VDD), LED144.1 (VDD), LED145.1 (VDD), LED146.1 (VDD), LED147.1 (VDD), LED148.1 (VDD), LED149.1 (VDD), LED150.1 (VDD), LED151.1 (VDD), LED152.1 (VDD), LED153.1 (VDD), LED154.1 (VDD), LED155.1 (VDD), LED156.1 (VDD), LED157.1 (VDD), LED158.1 (VDD), LED159.1 (VDD), LED160.1 (VDD), LED161.1 (VDD), LED162.1 (VDD), LED163.1 (VDD), LED164.1 (VDD), LED165.1 (VDD), LED166.1 (VDD), LED167.1 (VDD), LED168.1 (VDD), LED169.1 (VDD), LED170.1 (VDD), LED171.1 (VDD), LED172.1 (VDD), LED173.1 (VDD), LED174.1 (VDD), LED175.1 (VDD), LED176.1 (VDD), LED177.1 (VDD), LED178.1 (VDD), LED179.1 (VDD), LED180.1 (VDD), LED181.1 (VDD), LED182.1 (VDD)
